NicolasMiranda29/Project-Team-A2/INTRODUCTION TO ROBOTICS/CAD Files/CAD robots Parts/part 42.stp

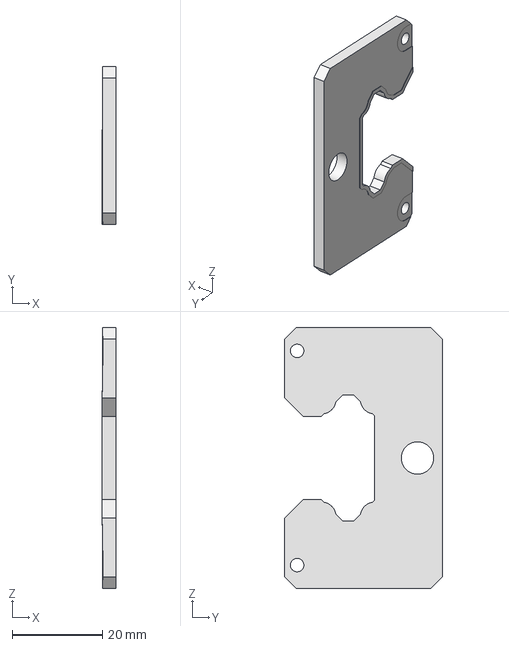
[picture p21: CAD file, 2025-12-10]
INTRODUCTION TO ROBOTICS/CAD Files/CAD robots Parts/part 42.stp
3.20 x 35.0 x 58.0 mm
