NicolasMiranda29/Project-Team-A2/INTRODUCTION TO ROBOTICS/CAD Files/CAD robots Parts/part 25.SLDPRT

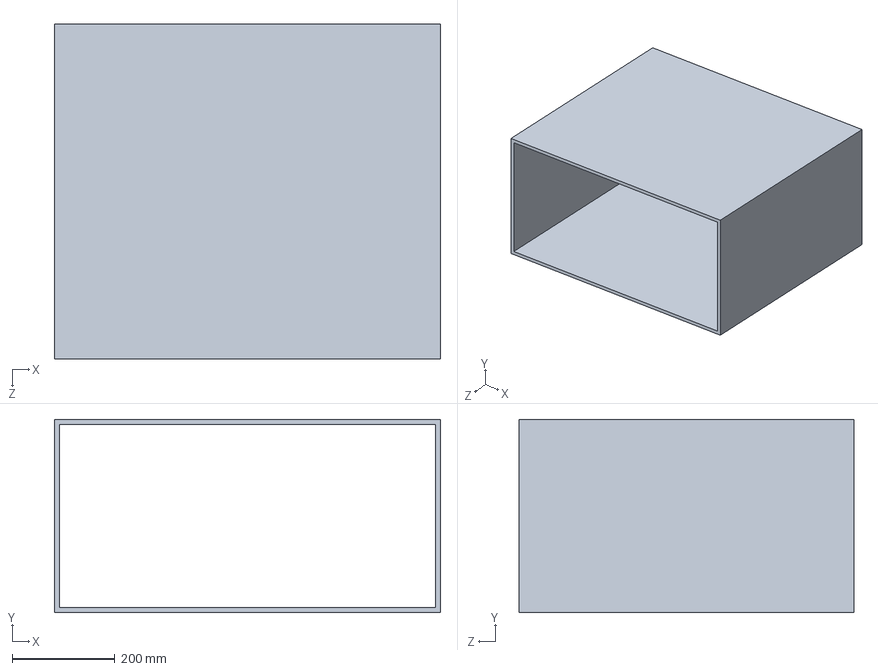
[picture p22: CAD file, 2025-12-10]
INTRODUCTION TO ROBOTICS/CAD Files/CAD robots Parts/part 25.SLDPRT
750.0 x 375.0 x 650.0 mm
