NicolasMiranda29/Project-Team-A2/INTRODUCTION TO ROBOTICS/CAD Files/CAD robots Parts/part 13.stp

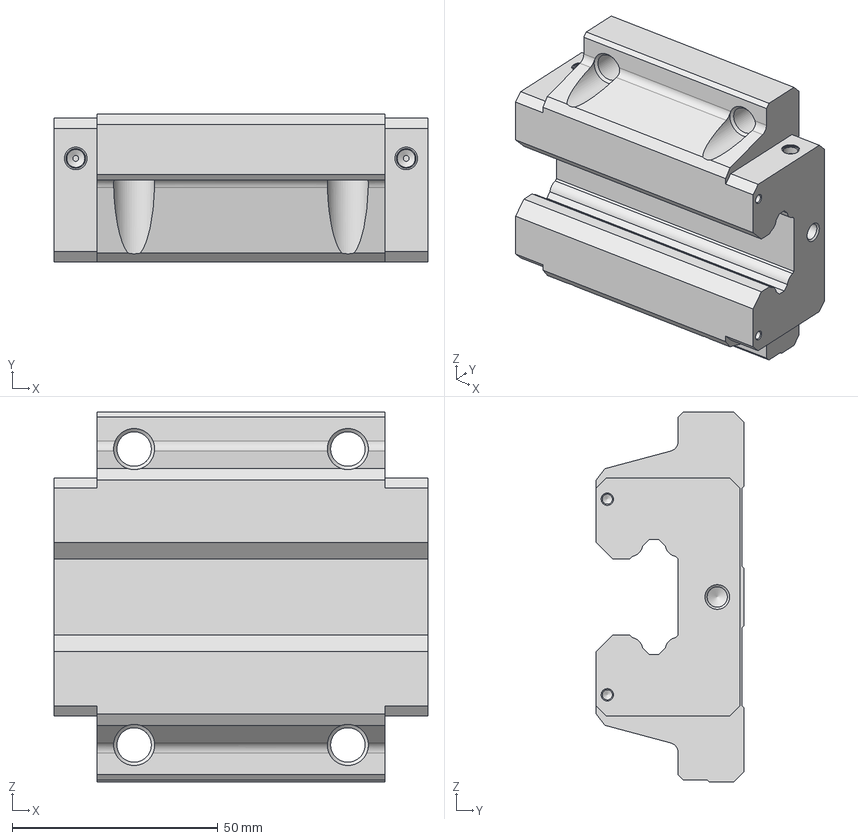
[picture p23: CAD file, 2025-12-10]
INTRODUCTION TO ROBOTICS/CAD Files/CAD robots Parts/part 13.stp
91.0 x 36.0 x 90.0 mm
