NicolasMiranda29/Project-Team-A2/INTRODUCTION TO ROBOTICS/CAD Files/CAD robots Parts/part 32.SLDPRT

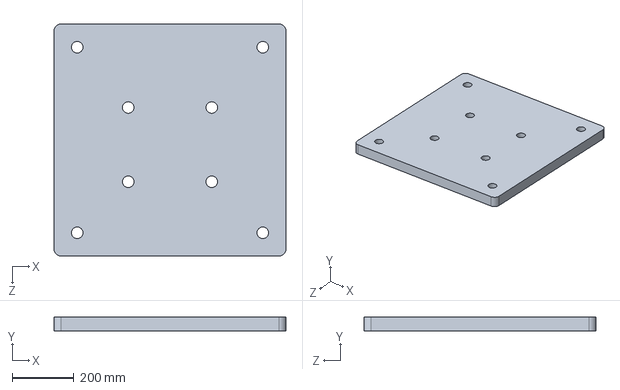
[picture p24: CAD file, 2025-12-10]
INTRODUCTION TO ROBOTICS/CAD Files/CAD robots Parts/part 32.SLDPRT
750.0 x 45.0 x 750.0 mm
