NicolasMiranda29/Project-Team-A2/INTRODUCTION TO ROBOTICS/CAD Files/CAD robots Parts/part 44.sldprt

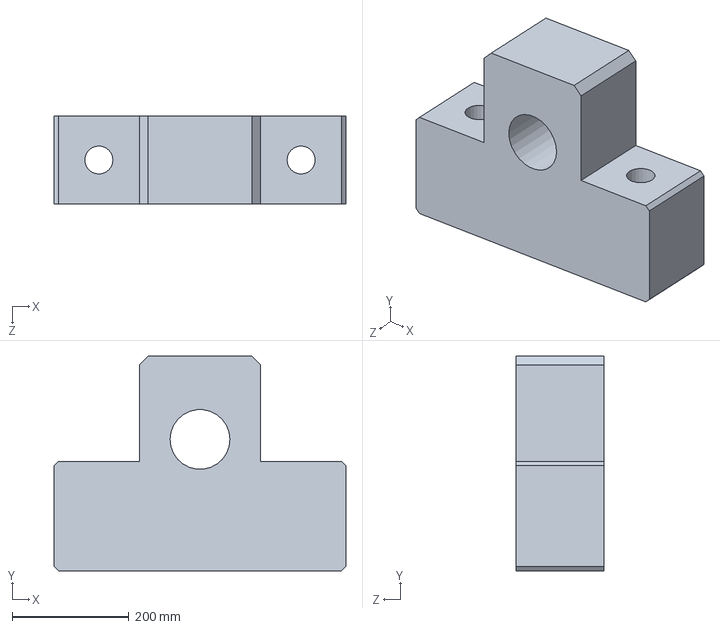
[picture p25: CAD file, 2025-12-10]
INTRODUCTION TO ROBOTICS/CAD Files/CAD robots Parts/part 44.sldprt
500.0 x 367.5 x 150.0 mm
