NicolasMiranda29/Project-Team-A2/INTRODUCTION TO ROBOTICS/CAD Files/CAD robots Parts/Part 20.SLDPRT

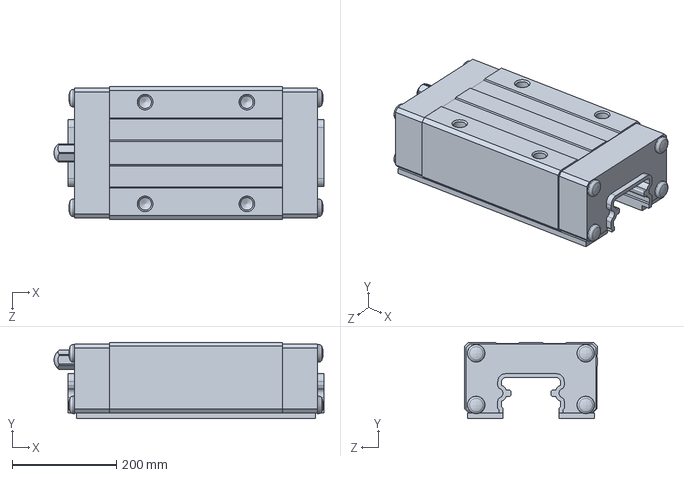
[picture p30: CAD file, 2025-12-10]
INTRODUCTION TO ROBOTICS/CAD Files/CAD robots Parts/Part 20.SLDPRT
517.3 x 146.2 x 255.0 mm
