NicolasMiranda29/Project-Team-A2/INTRODUCTION TO ROBOTICS/CAD Files/CAD robots Parts/Part 14.SLDPRT

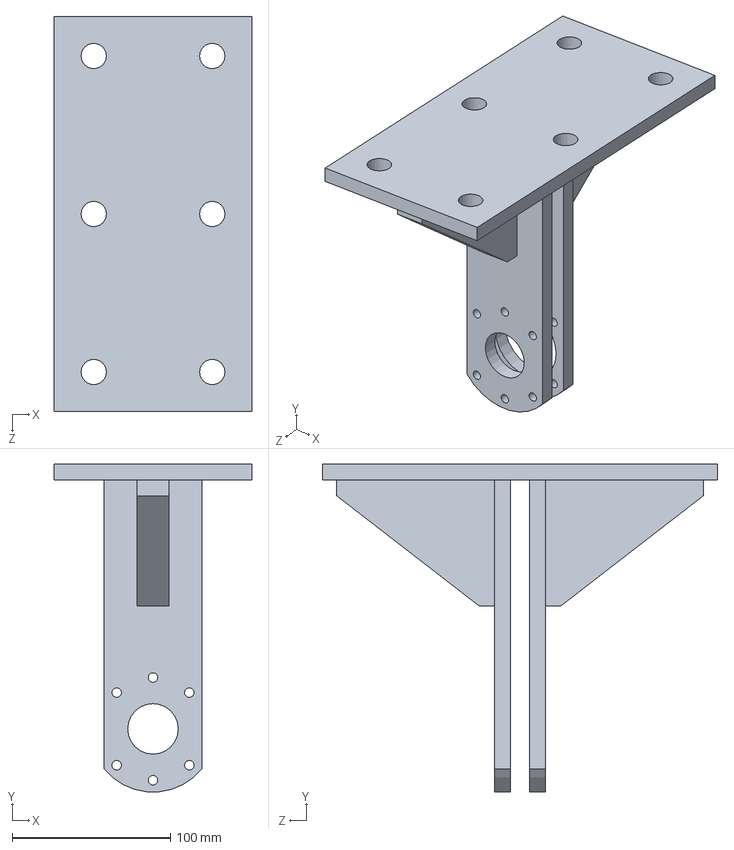
[picture p33: CAD file, 2025-12-10]
INTRODUCTION TO ROBOTICS/CAD Files/CAD robots Parts/Part 14.SLDPRT
125.0 x 207.3 x 250.0 mm
