NicolasMiranda29/Project-Team-A2/INTRODUCTION TO ROBOTICS/CAD Files/CAD robots Parts/Part 18.sldprt

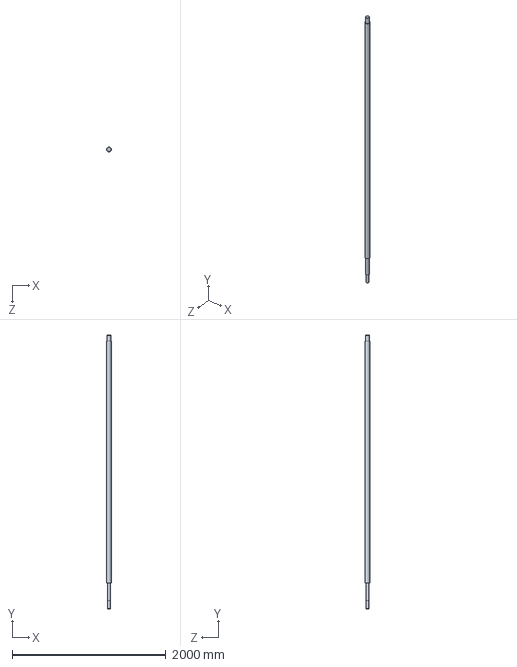
[picture p34: CAD file, 2025-12-10]
INTRODUCTION TO ROBOTICS/CAD Files/CAD robots Parts/Part 18.sldprt
64.0 x 3570.0 x 64.0 mm
