NicolasMiranda29/Project-Team-A2/INTRODUCTION TO ROBOTICS/CAD Files/CAD robots Parts/Part 10.SLDPRT

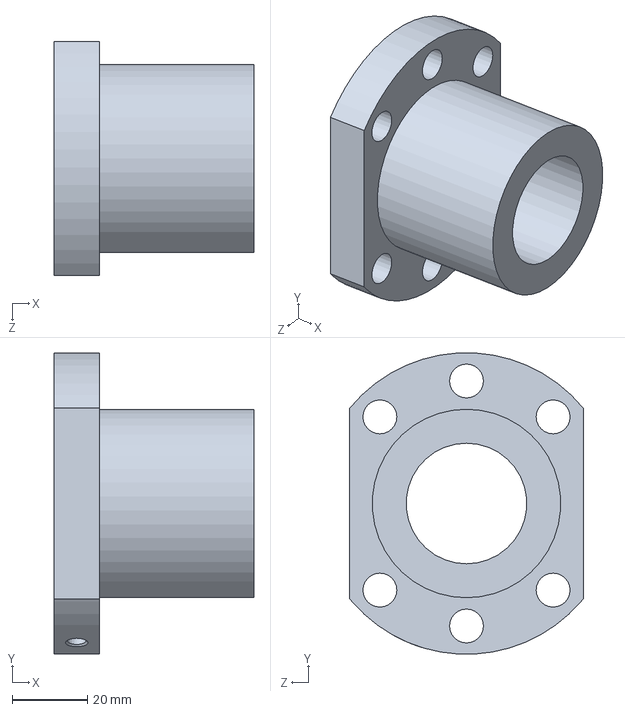
[picture p36: CAD file, 2025-12-10]
INTRODUCTION TO ROBOTICS/CAD Files/CAD robots Parts/Part 10.SLDPRT
53.0 x 79.9 x 62.0 mm
