NicolasMiranda29/Project-Team-A2/INTRODUCTION TO ROBOTICS/CAD Files/CAD robots Parts/Part 2.SLDPRT

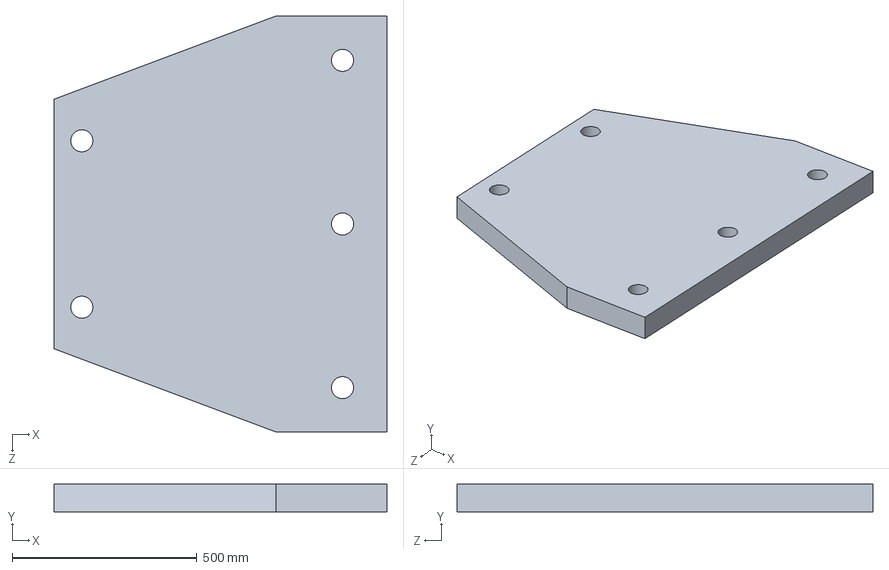
[picture p37: CAD file, 2025-12-10]
INTRODUCTION TO ROBOTICS/CAD Files/CAD robots Parts/Part 2.SLDPRT
900.0 x 75.0 x 1125.0 mm
